dalethomas81/HamMessenger/Media/Board-v1.1/IMG_4246.jpeg

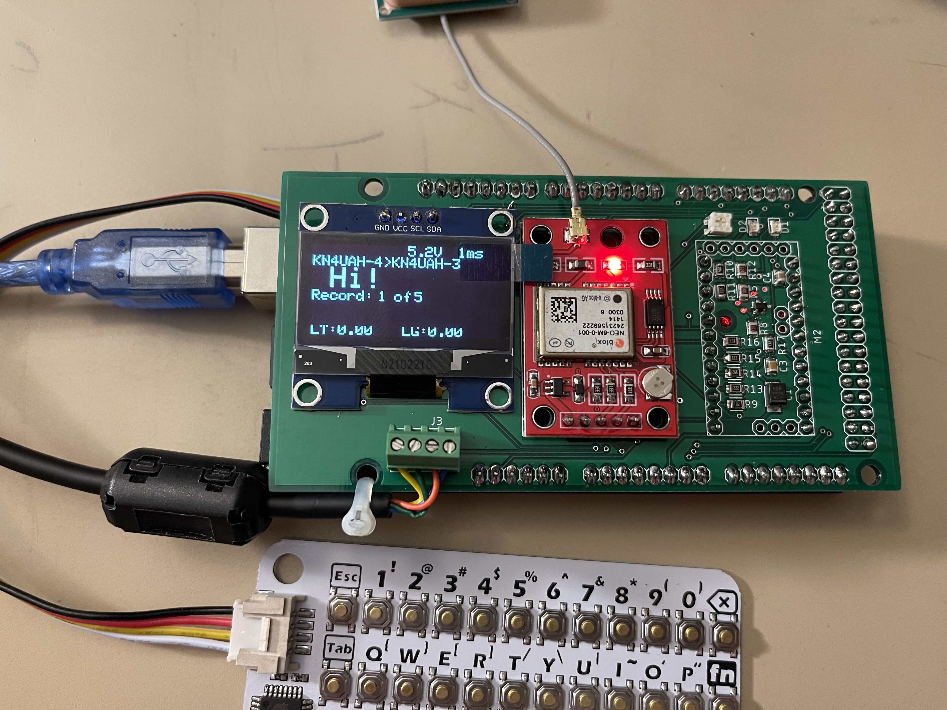
Media/Board-v1.1/IMG_4246.jpeg
