dalethomas81/HamMessenger/Media/Board-v1.1/IMG_4265.jpeg

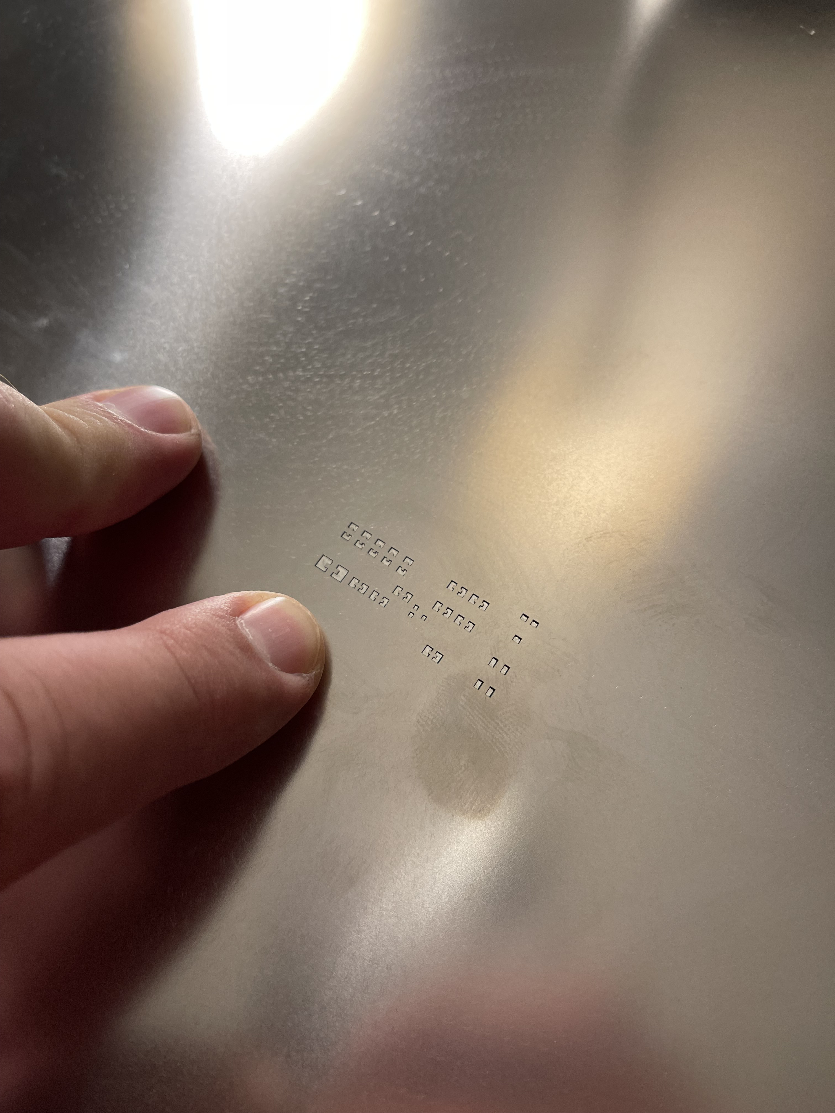
Media/Board-v1.1/IMG_4265.jpeg
