dalethomas81/HamMessenger/Media/CAD/Isometric.png

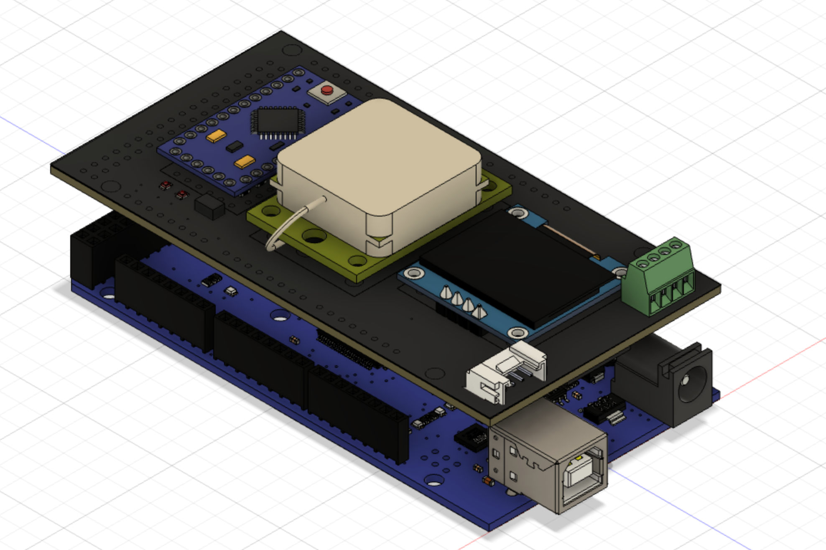
Media/CAD/Isometric.png
