dalethomas81/HamMessenger/Media/Illustration-Light.jpeg

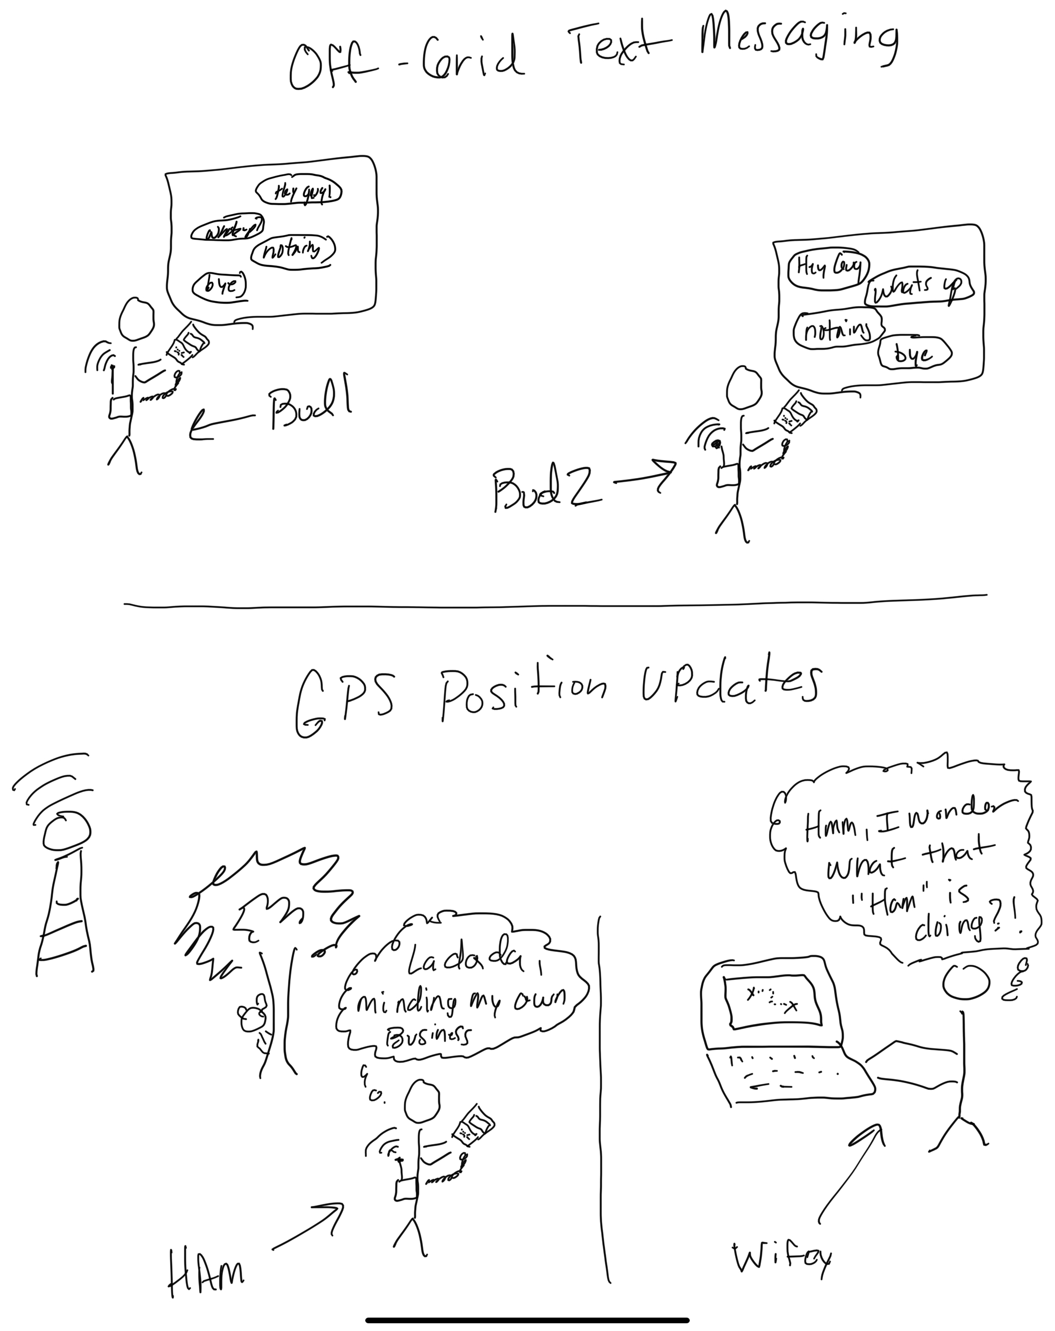
Media/Illustration-Light.jpeg
