dalethomas81/HamMessenger/Media/IMG_3985.jpeg

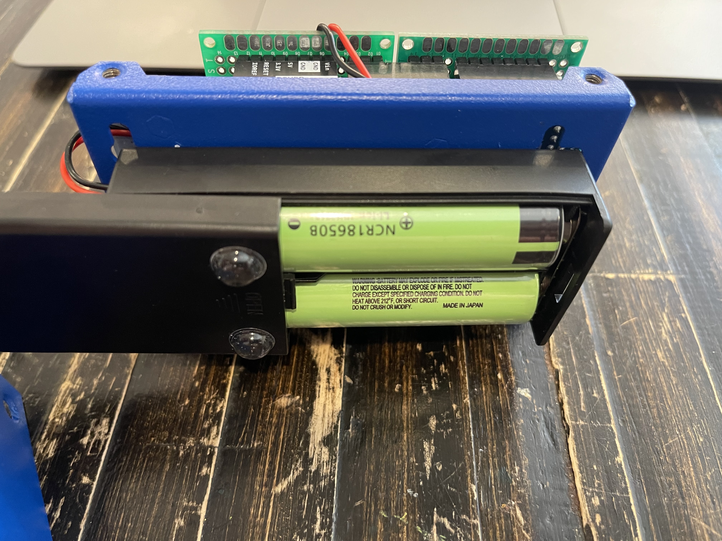
Media/IMG_3985.jpeg
