dalethomas81/HamMessenger/Media/IMG_4012.jpeg

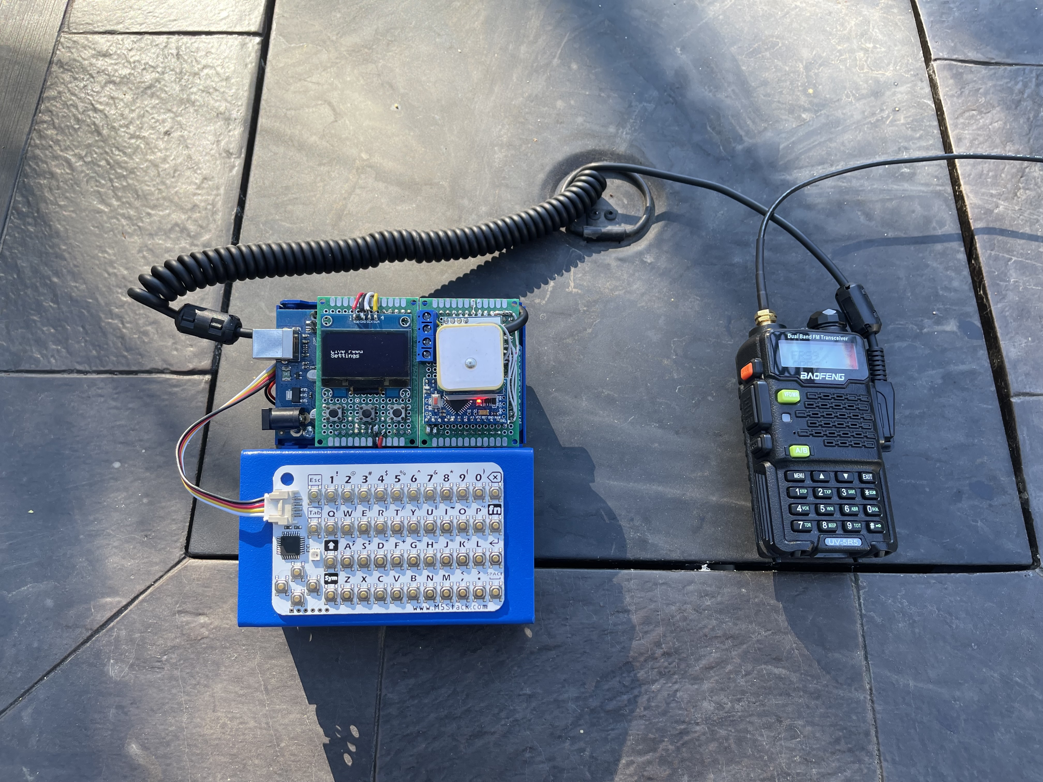
Media/IMG_4012.jpeg
