dalethomas81/HamMessenger/Media/Prototype-Table-Single.jpeg

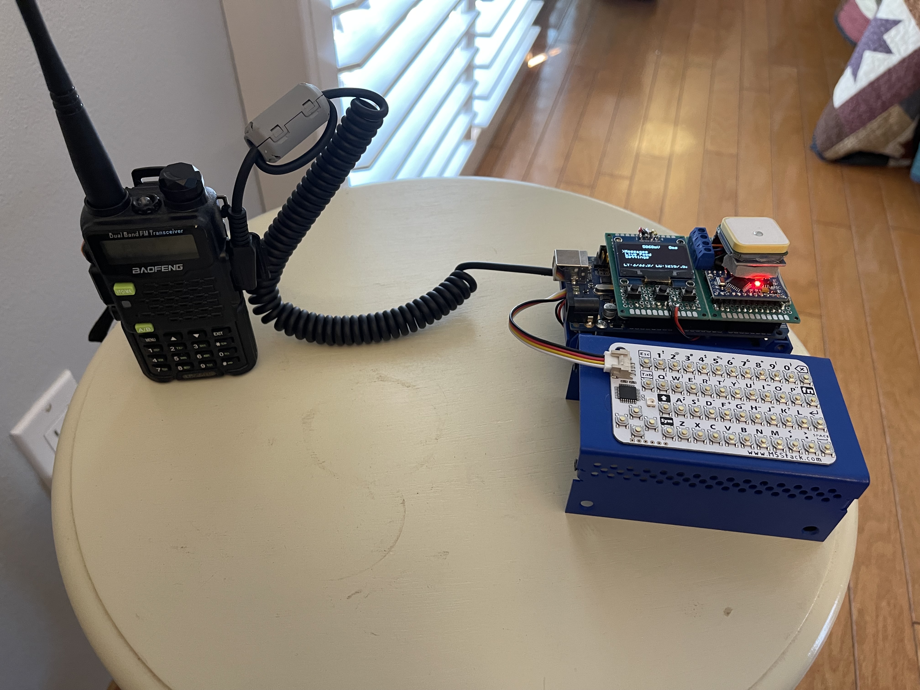
Media/Prototype-Table-Single.jpeg
