dalethomas81/HamMessenger/Media/Screenshots/LiveFeed.jpeg

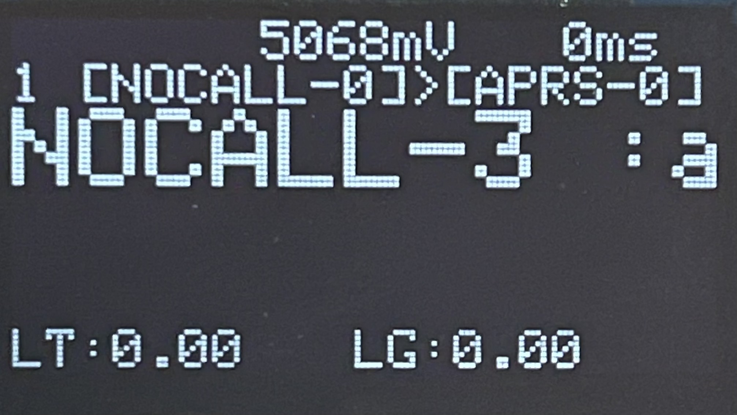
Media/Screenshots/LiveFeed.jpeg
