dalethomas81/HamMessenger/Media/Screenshots/Messages.jpeg

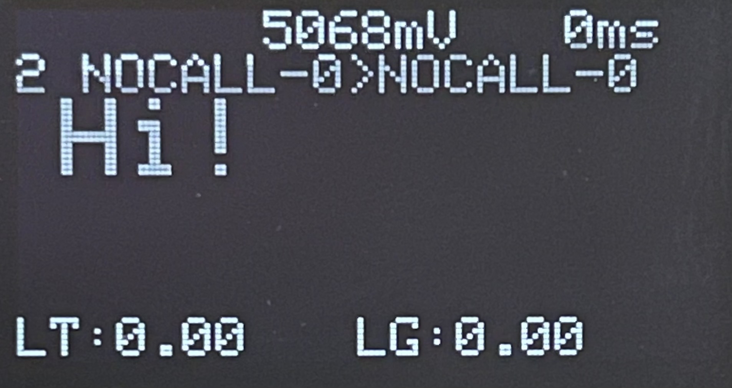
Media/Screenshots/Messages.jpeg
