dalethomas81/HamMessenger/Media/Screenshots/Messages_Empty.jpeg

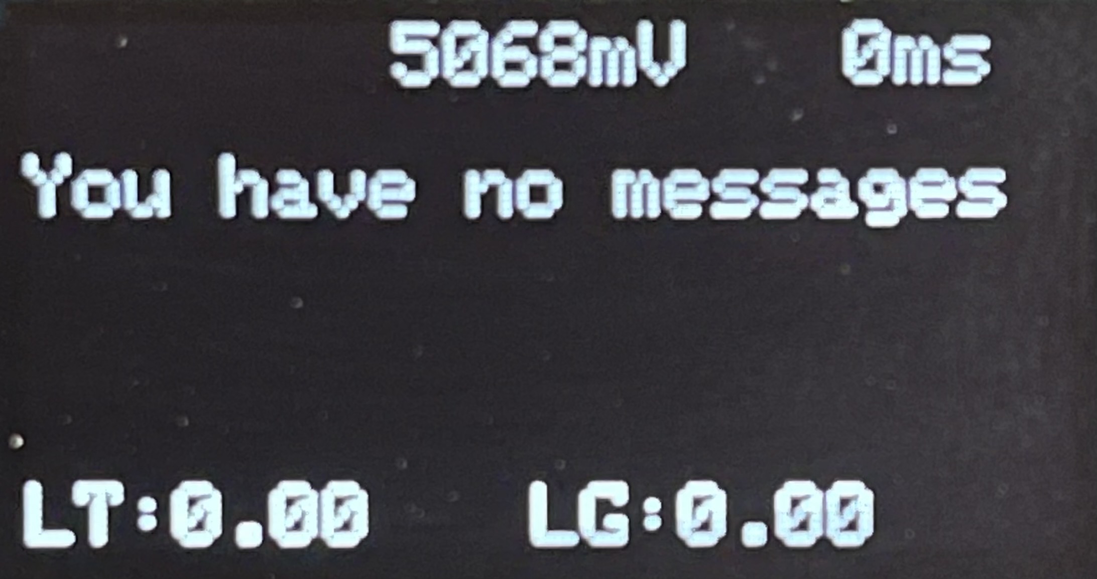
Media/Screenshots/Messages_Empty.jpeg
