dalethomas81/HamMessenger/Media/Screenshots/Settings.jpeg

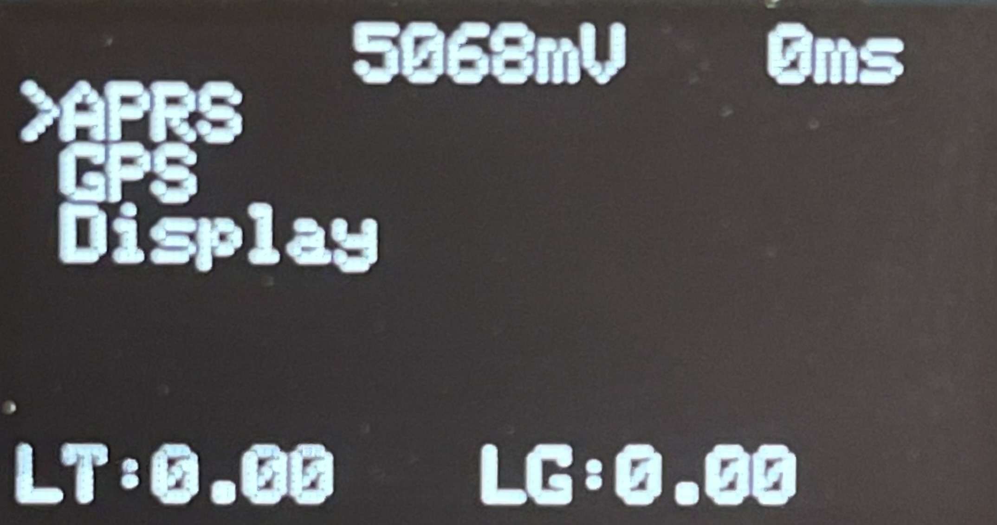
Media/Screenshots/Settings.jpeg
