dalethomas81/HamMessenger/Media/Screenshots/Settings_APRS.jpeg

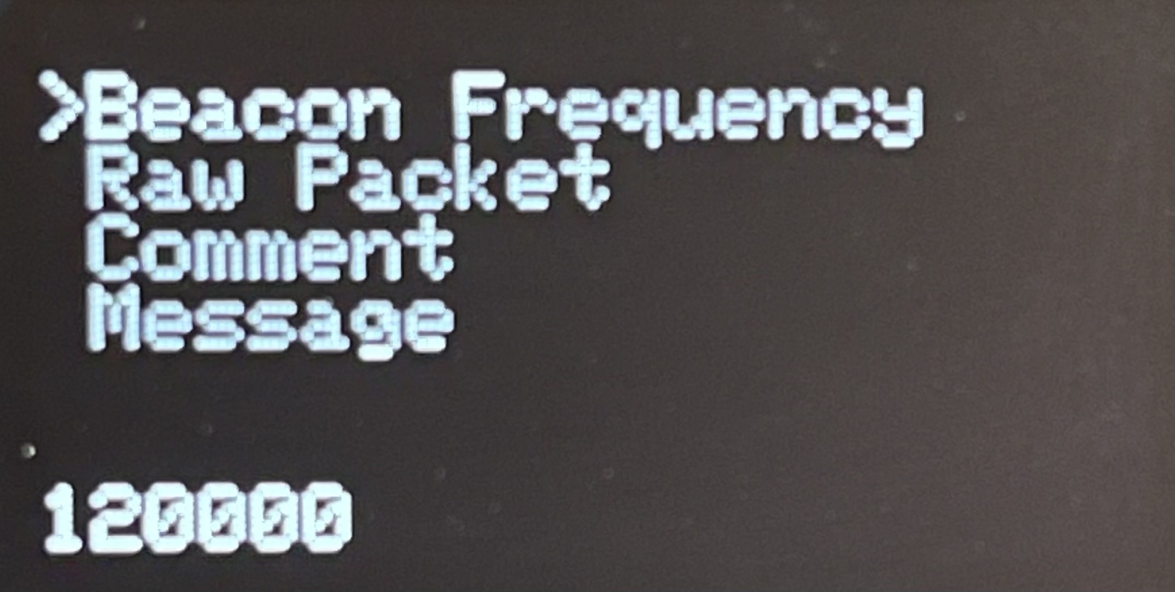
Media/Screenshots/Settings_APRS.jpeg
