dalethomas81/HamMessenger/Media/Screenshots/Settings_Display.jpeg

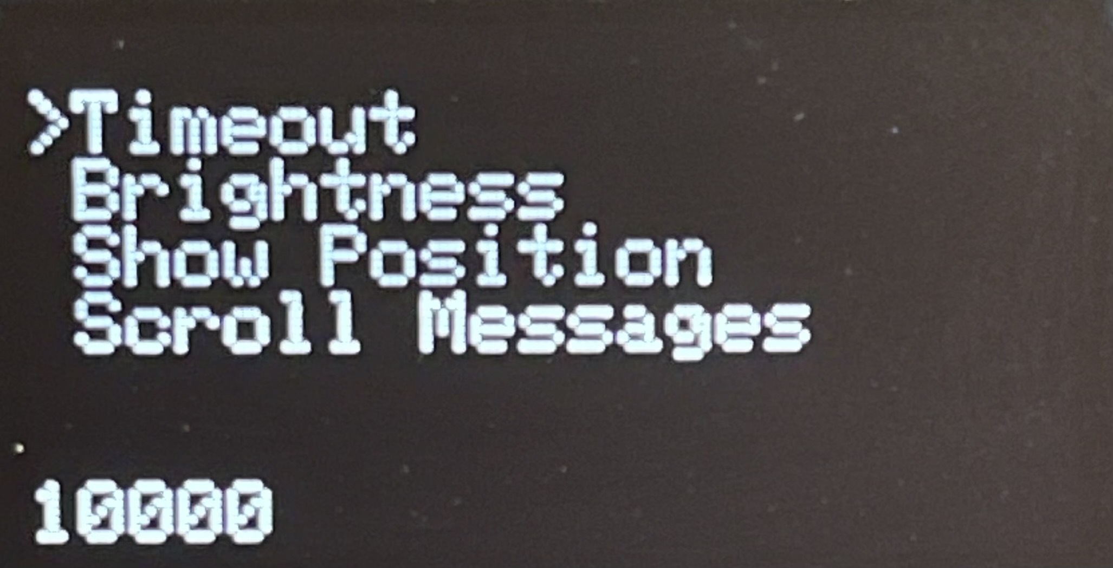
Media/Screenshots/Settings_Display.jpeg
