dalethomas81/HamMessenger/Media/Screenshots/Settings_Save.jpeg

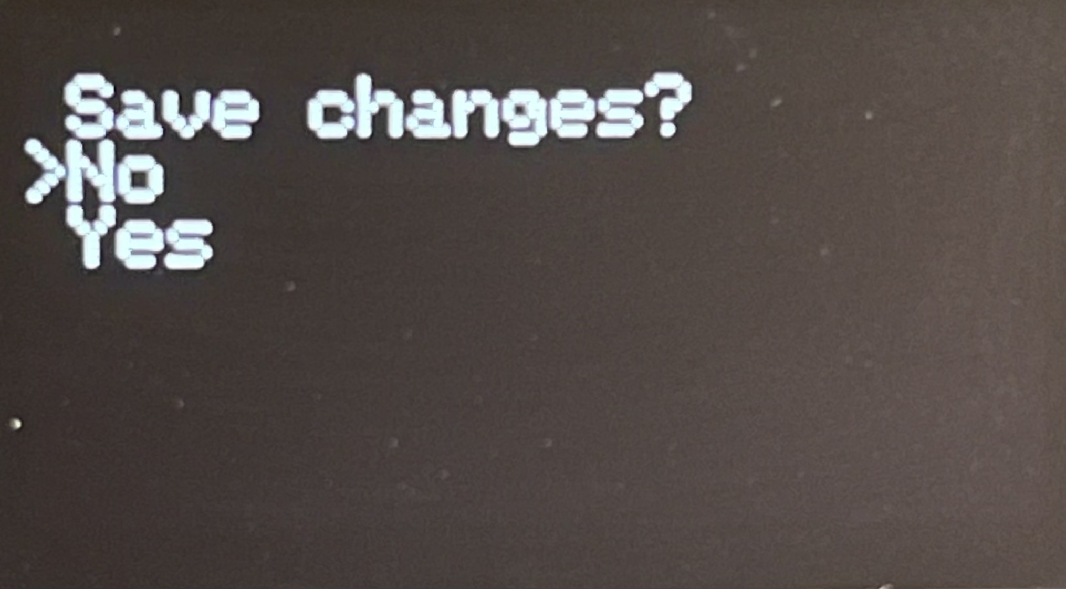
Media/Screenshots/Settings_Save.jpeg
