dalethomas81/HamMessenger/Media/Unibody-Frame-v1/back.jpeg

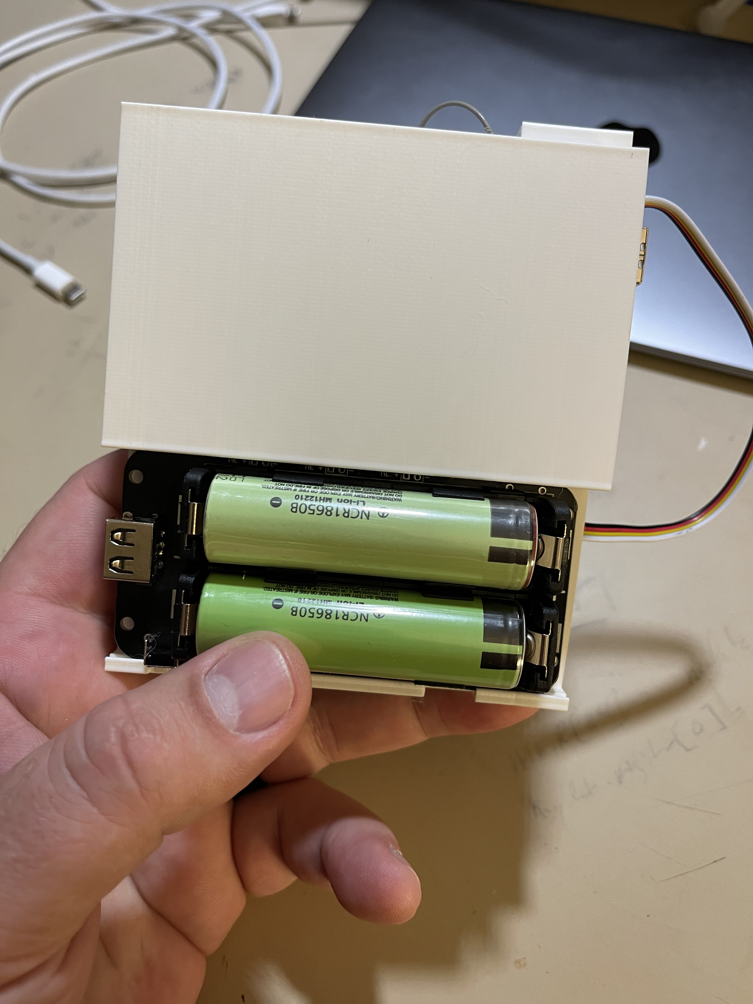
Media/Unibody-Frame-v1/back.jpeg
