dalethomas81/HamMessenger/Media/Unibody-Frame-v1/cura.png

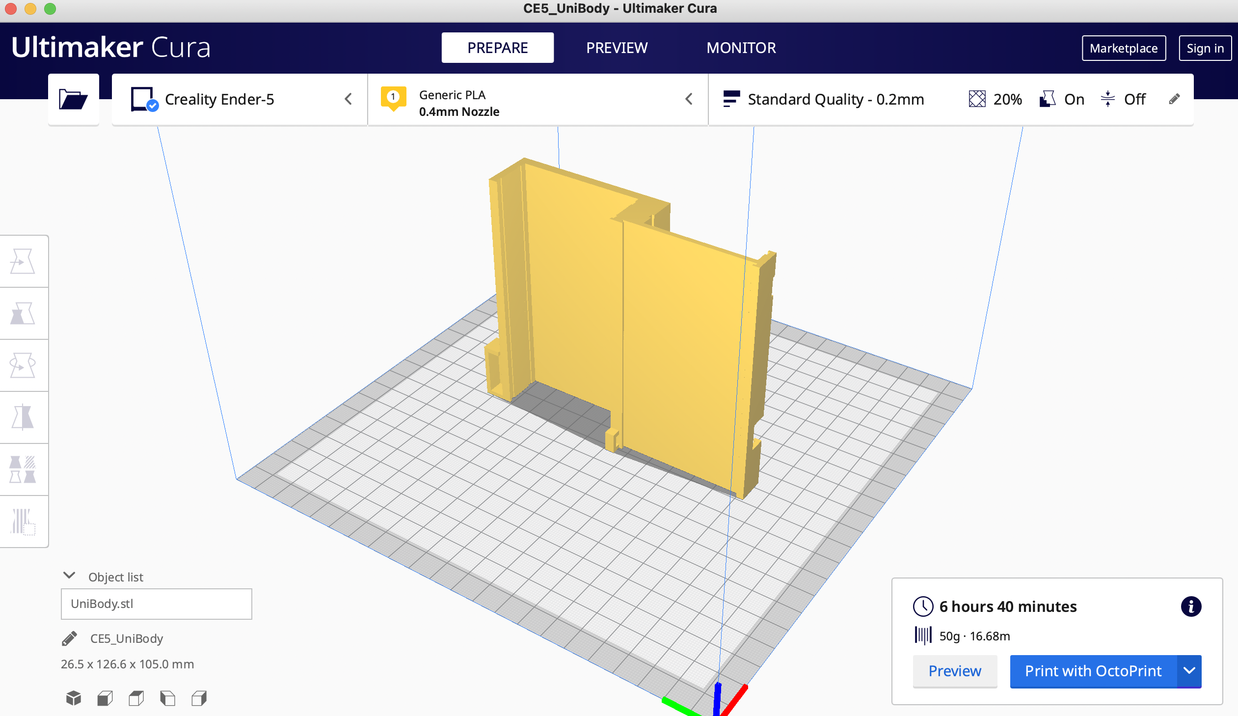
Media/Unibody-Frame-v1/cura.png
