dalethomas81/HamMessenger/Media/Unibody-Frame-v1/front.jpeg

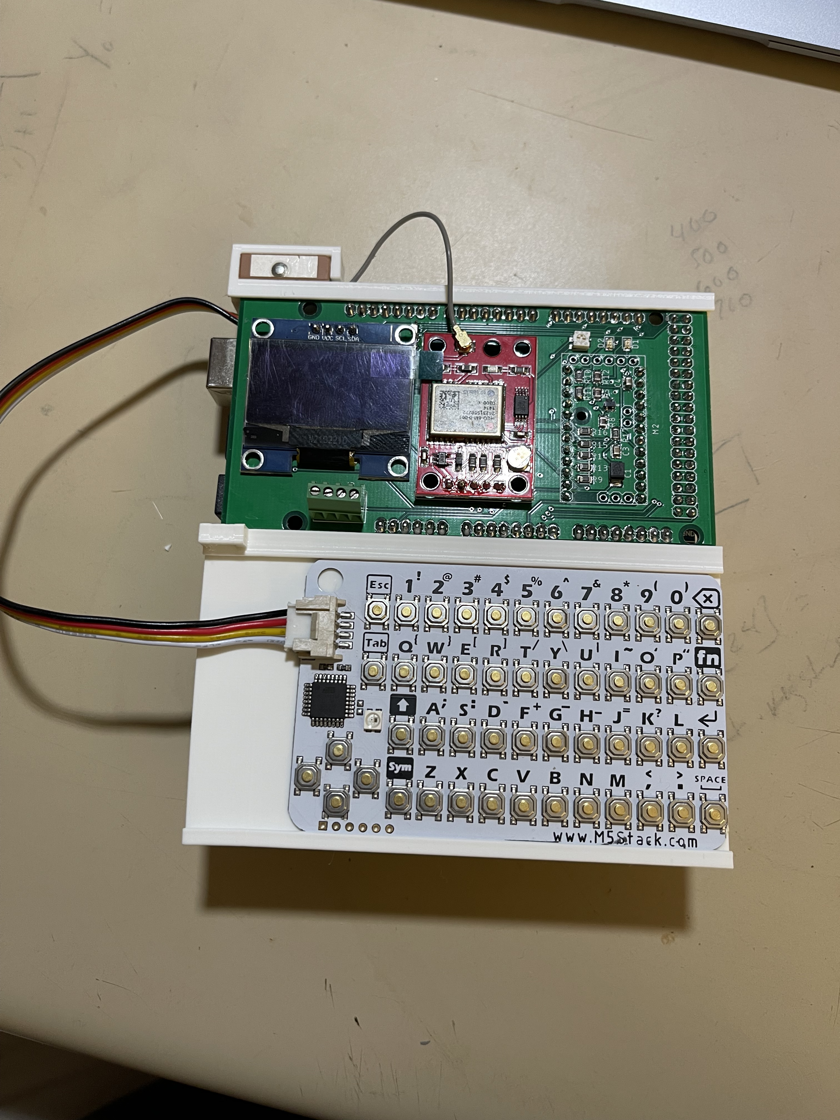
Media/Unibody-Frame-v1/front.jpeg
