dalethomas81/HamMessenger/Media/Unibody-Frame-v1/side.jpeg

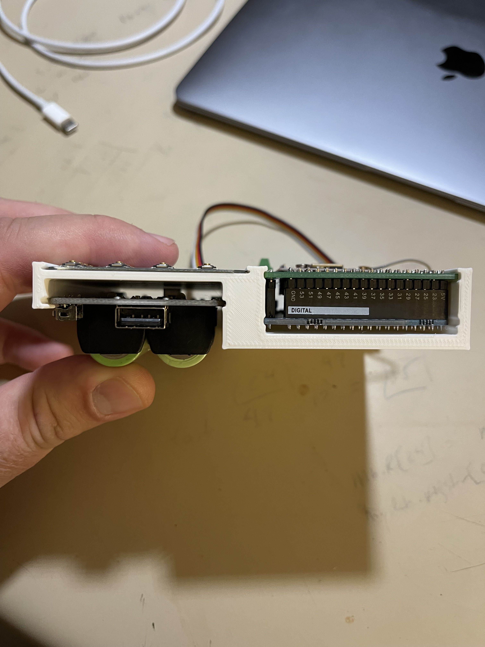
Media/Unibody-Frame-v1/side.jpeg
