dalethomas81/HamMessenger/Media/Board-v1.1/IMG_4268.jpeg

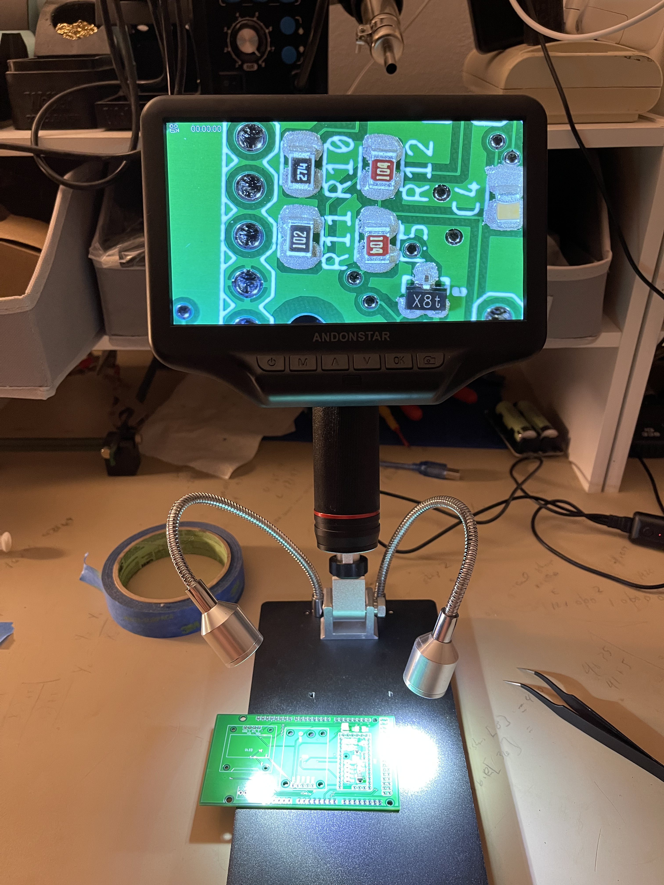
Media/Board-v1.1/IMG_4268.jpeg
