dalethomas81/HamMessenger/Media/IMG_3983.jpeg

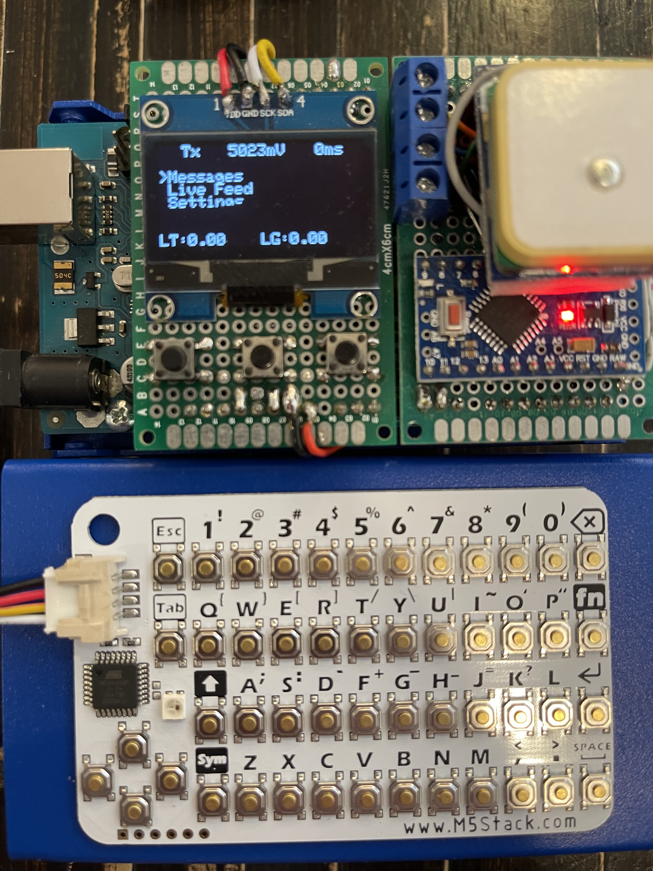
Media/IMG_3983.jpeg
