dalethomas81/HamMessenger/Media/IMG_3986.jpeg

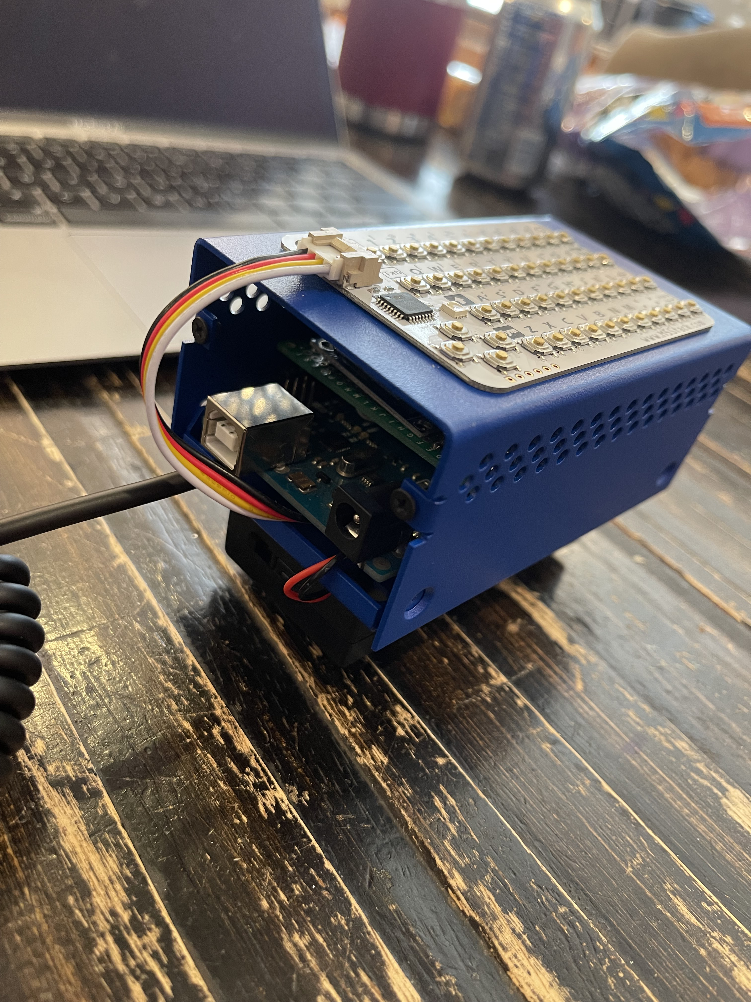
Media/IMG_3986.jpeg
