dalethomas81/HamMessenger/Media/IMG_4013.jpeg

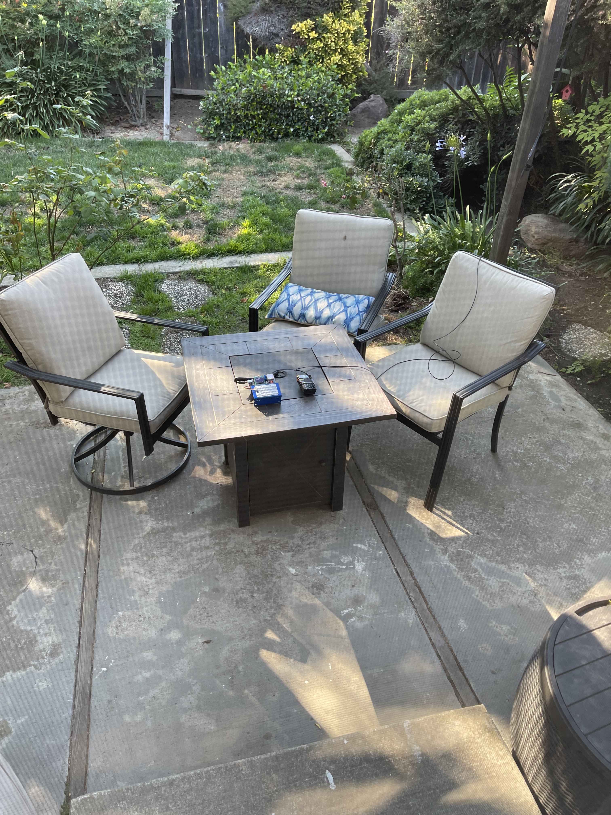
Media/IMG_4013.jpeg
