dalethomas81/HamMessenger/Media/Prototype-Table-Double.jpeg

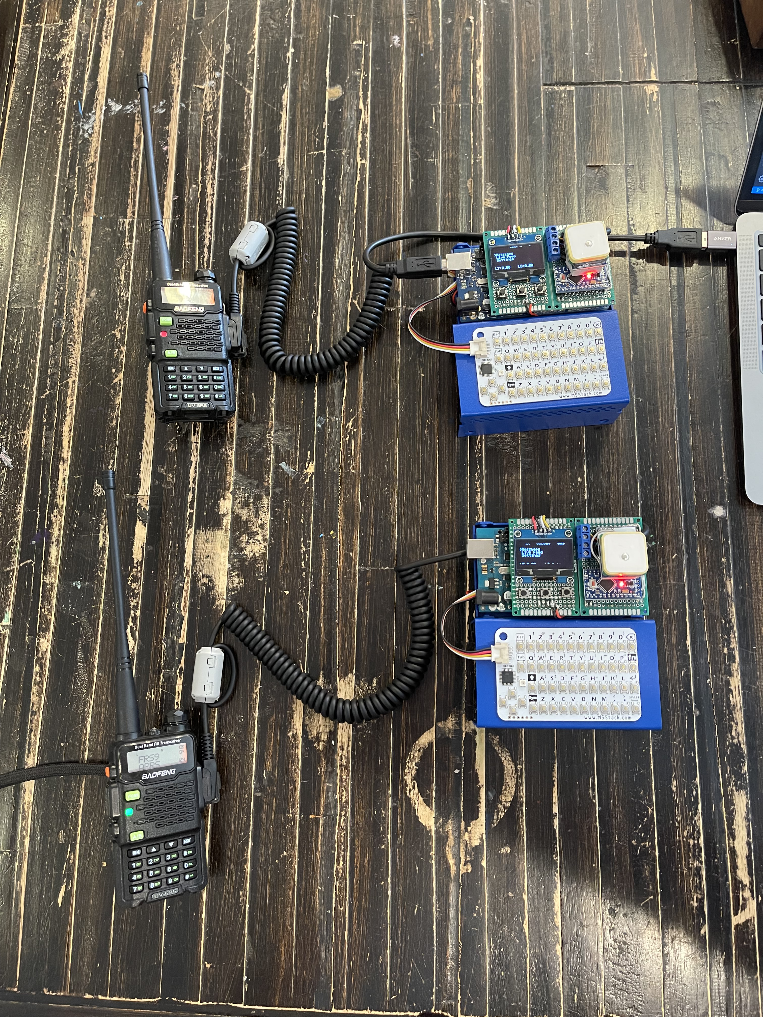
Media/Prototype-Table-Double.jpeg
